tinkerspy/pinball/diptrace/png/controller02-pcb.png

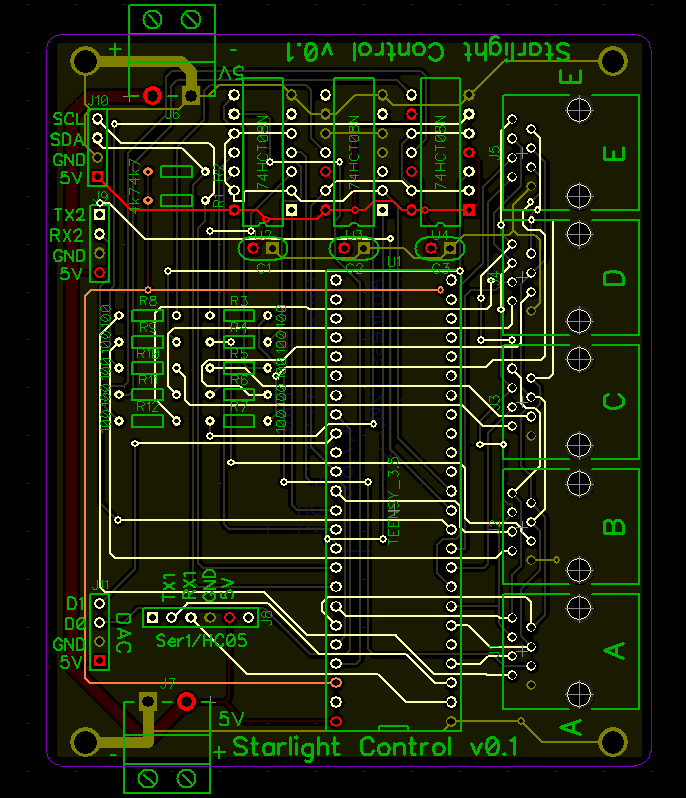
diptrace/png/controller02-pcb.png
