tinkerspy/pinball/diptrace/png/switchnodexl02-pcb.png

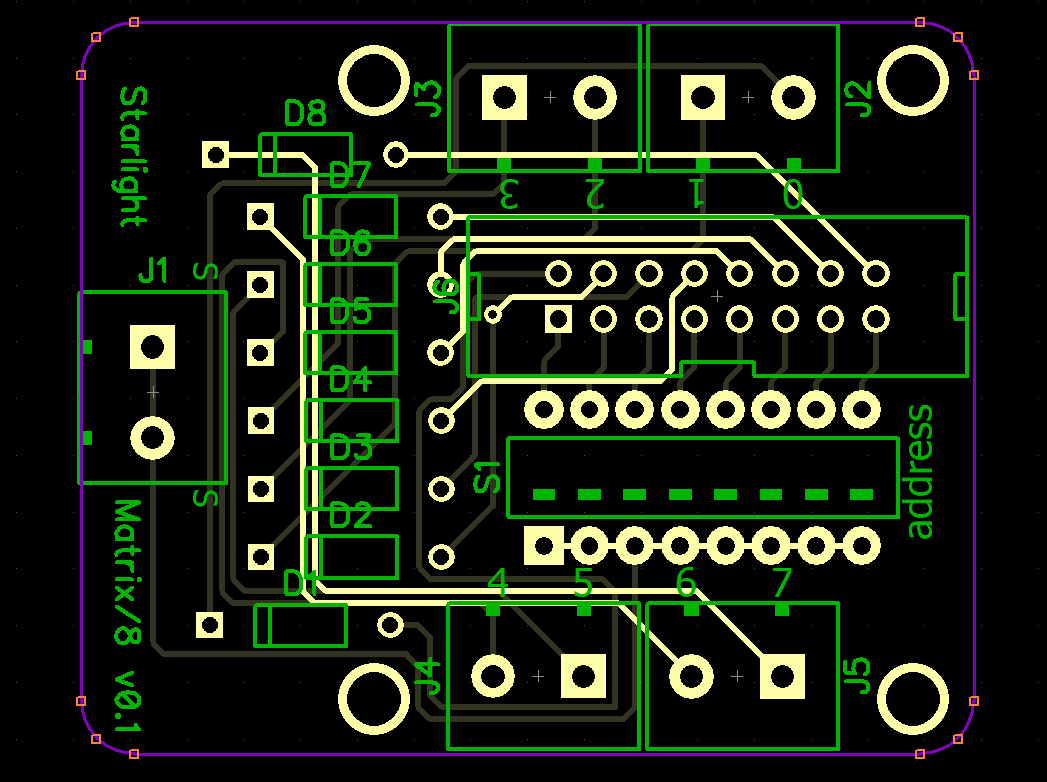
diptrace/png/switchnodexl02-pcb.png
