tinkerspy/pinball/firmware_custom.h

#pragma once

/* Custom firmware for the Atm_device programmable pinball device class
 *  
 *  tictactoe
 *  
 *  playfield.device( <switch-id> ); // Instantiates object
 *  playfield.device( <switch-id>, <led-id>, <firmware> ); // Initializes object
 *  
 */

namespace custom_firmware {

const char game_bytecode[] = R""""(
init, press_start, release_start, ball_exit, sub_wait_players, sub_wait_reset, sub_loop, \
sub_ball_loop, sub_player_loop, sub_core, sub_wait_playing, sub_wait_collecting, sub_press_start
out_init, out_enable, out_counter_reset, out_players_zero, out_ball_zero,\
out_player_zero, out_ball_adv, out_player_adv, out_3bonus, out_collect,\
out_kickoff, out_over, out_players_adv, out_disable, out_release
arg_collecting, arg_again, arg_counter0, arg_counter1,\
arg_counter2, arg_counter3, arg_counter4, arg_counter5
reg_state, reg_max_players, reg_no_of_players, reg_player, reg_no_of_balls,\
reg_ball, reg_ball_cntr
msg_init, msg_wait_start, msg_ball_loop, msg_player_loop, msg_counter_reset, msg_add_player


// TODO tilt!
sub_press_start
R, -1, -1, reg_ball_cntr       // Exit if we're already in play
>,  0, -1, 0
R, -1, -1, reg_no_of_players   // Exit 
=,  6,  0, 2
R, -1, -1, reg_max_players 
=,  6, -1, 0
R, -1, -1, reg_no_of_players
=,  5,  0, 2
R, -1, -1, reg_max_players
=,  5, -1, 0
R, -1, -1, reg_no_of_players
=,  4,  0, 2
R, -1, -1, reg_max_players
=,  4, -1, 0
R, -1, -1, reg_no_of_players
=,  3,  0, 2
R, -1, -1, reg_max_players
=,  3, -1, 0
R, -1, -1, reg_no_of_players
=,  2,  0, 2
R, -1, -1, reg_max_players
=,  2, -1, 0
R, -1, -1, reg_no_of_players
=,  1,  0, 2
R, -1, -1, reg_max_players
=,  1, -1, 0
R, -1, -1, reg_no_of_players
T, -1, -1, out_players_adv
I, -1, -1, 1
Q, reg_no_of_players, -1, msg_add_player;

init
T, -1, -1, out_init             
W, -1, -1, 100                
R, -1, -1, 0
D, -1, -1, reg_no_of_balls
R, -1, -1, 1
D, -1, -1, reg_max_players
R, -1, -1, 0
Z, -1, -1, 0
A, -1, -1, sub_loop;

sub_loop
T, -1, -1, out_over
R, -1, -1, reg_ball_cntr
Z, -1, -1, 0
R, -1, -1, reg_no_of_players
Z, -1, -1, 0
E, press_start, 0, 0            // Clear press event
Q, -1, -1, msg_wait_start
S, -1, -1, sub_wait_players     // Wait for a front button press to start game
W, -1, -1, 100
Q, -1, -1, msg_init
T, -1, -1, out_init
T, -1, -1, out_players_zero
T, -1, -1, out_ball_zero
T, -1, -1, out_counter_reset
S, -1, -1, sub_wait_reset
R, -1, -1, reg_no_of_balls
D, -1, -1, reg_ball
T, -1, -1, out_player_zero
S, -1, -1, sub_ball_loop
A, -1, -1, sub_loop;

sub_ball_loop
Q, reg_ball, -1, msg_ball_loop
R, -1, -1, reg_no_of_players
D, -1, -1, reg_player
T, -1, -1, out_player_zero
W, -1, -1, 11
S, -1, -1, sub_player_loop
W, -1, -1, 12
R, -1, -1, reg_ball
I, -1, -1, -1
=,  0, -1, 0
T, -1, -1, out_ball_adv
A, -1, -1, sub_ball_loop;

sub_player_loop
Q, reg_player, -1, msg_player_loop
S, -1, -1, sub_core
J, arg_again, -2, 0
R, -1, -1, reg_player
I, -1, -1, -1
=,  0, -1, 0
T, -1, -1, out_player_adv
A, -1, -1, sub_player_loop;

sub_core
W, -1, -1, 500
R, -1, -1, reg_ball
T,  1,  out_3bonus, -1
T, -1, -1, out_init
W, -1, -1, 100
T, -1, -1, out_kickoff
W, -1, -1, 1000
T, -1, -1, out_enable
W, -1, -1, 100
E, ball_exit, 0, 0                // Clear press_exit event
S, -1, -1, sub_wait_playing
T, -1, -1, out_disable
T, -1, -1, out_release
W, -1, -1, 100
T, -1, -1, out_collect
W, -1, -1, 100
S, -1, -1, sub_wait_collecting
W, -1, -1, 100
R, -1, -1, reg_ball_cntr
I, -1, -1, 1
=,  1,  0, -1
R, -1, -1, reg_no_of_players
D, -1, -1, reg_player;

sub_wait_players
R, -1, -1, reg_no_of_players
W, -1, -1, 0
E, press_start, 0, 2                // On event set no of players to 1
Z, -1, -1, 1
J, -1, -1, -1                       // and exit sub
A, -1, -1, sub_wait_players;        // else keep looping

sub_wait_reset                      // busy loop: waiting for counter reset to finish
Q, reg_max_players, -1, msg_counter_reset
W, -1, -1, 100
E, press_start, 0, 1                // On event increment no of players
S, -1, -1, sub_press_start
J, arg_counter0, -4, 0
J, arg_counter1, -5, 0
J, arg_counter2, -6, 0
J, arg_counter3, -7, 0
J, arg_counter4, -8, 0
J, arg_counter5, -9, 0;

sub_wait_playing                    // Central game loop: process ball_exit & frontbtn press
R, -1, -1, reg_no_of_players
W, -1, -1, 0
E, press_start, 0, 1                // On event set no of players to 1
S, -1, -1, sub_press_start
E, ball_exit, -1, -4;

sub_wait_collecting
W, -1, -1, 100
J, arg_collecting, -2, -1;
)"""";

const char std_game_symbin[] = {
  "\x78\x56\x34\x12\xb0\x00\x00\x00" "init\0press_start\0release_start\0ball_exit\0sub_wait_players\0sub_wait_reset\0sub_loop\0sub_ball_loop\0sub_player_loop\0sub_core\0sub_wait_playing\0sub_wait_collecting\0sub_press_start\0\0\0"
  "\x78\x56\x34\x12\xc8\x00\x00\x00" "out_init\0out_enable\0out_counter_reset\0out_players_zero\0out_ball_zero\0out_player_zero\0out_ball_adv\0out_player_adv\0out_3bonus\0out_collect\0out_kickoff\0out_over\0out_players_adv\0out_disable\0out_release\0\0\0\0"
  "\x78\x56\x34\x12\x68\x00\x00\x00" "arg_collecting\0arg_again\0arg_counter0\0arg_counter1\0arg_counter2\0arg_counter3\0arg_counter4\0arg_counter5\0\0"
  "\x78\x56\x34\x12\x60\x00\x00\x00" "reg_state\0reg_max_players\0reg_no_of_players\0reg_player\0reg_no_of_balls\0reg_ball\0reg_ball_cntr\0\0\0"
  "\x00\x00\x00\x00\x00\x00\x00\x00" "msg_init\0msg_wait_start\0msg_ball_loop\0msg_player_loop\0msg_counter_reset\0msg_add_player\0\0"
};

const uint16_t std_game_hexbin[] = {
  0x0089, 0x0000, 0x0000, 0x0000, 0x01B3, 0x01CD, 0x00AF, 0x0101, 0x0133, 0x0155, 0x01F7, 0x020D, 
  0x000F, 0xFFFF, 0x000C, 0x0052, 0xFFFF, 0xFFFF, 0x0006, 0x003E, 0x0000, 0xFFFF, 0x0000, 0x0052, 
  0xFFFF, 0xFFFF, 0x0002, 0x003D, 0x0006, 0x0000, 0x0002, 0x0052, 0xFFFF, 0xFFFF, 0x0001, 0x003D, 
  0x0006, 0xFFFF, 0x0000, 0x0052, 0xFFFF, 0xFFFF, 0x0002, 0x003D, 0x0005, 0x0000, 0x0002, 0x0052, 
  0xFFFF, 0xFFFF, 0x0001, 0x003D, 0x0005, 0xFFFF, 0x0000, 0x0052, 0xFFFF, 0xFFFF, 0x0002, 0x003D, 
  0x0004, 0x0000, 0x0002, 0x0052, 0xFFFF, 0xFFFF, 0x0001, 0x003D, 0x0004, 0xFFFF, 0x0000, 0x0052, 
  0xFFFF, 0xFFFF, 0x0002, 0x003D, 0x0003, 0x0000, 0x0002, 0x0052, 0xFFFF, 0xFFFF, 0x0001, 0x003D, 
  0x0003, 0xFFFF, 0x0000, 0x0052, 0xFFFF, 0xFFFF, 0x0002, 0x003D, 0x0002, 0x0000, 0x0002, 0x0052, 
  0xFFFF, 0xFFFF, 0x0001, 0x003D, 0x0002, 0xFFFF, 0x0000, 0x0052, 0xFFFF, 0xFFFF, 0x0002, 0x003D, 
  0x0001, 0x0000, 0x0002, 0x0052, 0xFFFF, 0xFFFF, 0x0001, 0x003D, 0x0001, 0xFFFF, 0x0000, 0x0052, 
  0xFFFF, 0xFFFF, 0x0002, 0x0054, 0xFFFF, 0xFFFF, 0x000C, 0x0049, 0xFFFF, 0xFFFF, 0x0001, 0x0051, 
  0x0002, 0xFFFF, 0x0005, 0xFFFF, 0x0000, 0x0054, 0xFFFF, 0xFFFF, 0x0000, 0x0057, 0xFFFF, 0xFFFF, 
  0x0064, 0x0052, 0xFFFF, 0xFFFF, 0x0000, 0x0044, 0xFFFF, 0xFFFF, 0x0004, 0x0052, 0xFFFF, 0xFFFF, 
  0x0001, 0x0044, 0xFFFF, 0xFFFF, 0x0001, 0x0052, 0xFFFF, 0xFFFF, 0x0000, 0x005A, 0xFFFF, 0xFFFF, 
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
  "\x78\x56\x34\x12\x28\x00\x00\x00" "init\0cycle\0sub_led0\0sub_led1\0sub_led2\0\0\0"
  "\x78\x56\x34\x12\x04\x00\x00\x00" "\0\0\0\0"
  "\x78\x56\x34\x12\x1c\x00\x00\x00" "arg_led0\0arg_led1\0arg_led2\0\0"
  "\x00\x00\x00\x00\x00\x00\x00\x00" "reg_t0\0reg_t1\0reg_t2\0\0"
};

const uint16_t std_animation_hexbin[] = {
  0x0007, 0x0019, 0x002F, 0x0051, 0x0073, 0xFFFF, 0x0000, 0x004C, 0xFFFF, 0xFFFF, 0x0000, 0x004C, 
  0xFFFF, 0xFFFF, 0x0001, 0x004C, 0xFFFF, 0xFFFF, 0x0002, 0x0041, 0xFFFF, 0xFFFF, 0x0001, 0xFFFF, 
  0x0001, 0x0057, 0xFFFF, 0xFFFF, 0x0064, 0x0053, 0xFFFF, 0xFFFF, 0x0002, 0x0053, 0xFFFF, 0xFFFF, 
  0x0003, 0x0053, 0xFFFF, 0xFFFF, 0x0004, 0x0041, 0xFFFF, 0xFFFF, 0x0001, 0xFFFF, 0x0002, 0x0052, 
  0xFFFF, 0xFFFF, 0x0000, 0x0049, 0xFFFF, 0xFFFF, 0xFFFF, 0x003C, 0x0001, 0x0000, 0xFFFF, 0x005A, 
  0xFFFF, 0xFFFF, 0x0008, 0x004A, 0x0000, 0x0000, 0x0002, 0x004C, 0xFFFF, 0xFFFF, 0x0000, 0x004A, 
  0xFFFF, 0xFFFF, 0xFFFF, 0x0048, 0xFFFF, 0xFFFF, 0x0000, 0xFFFF, 0x0003, 0x0052, 0xFFFF, 0xFFFF, 
  0x0001, 0x0049, 0xFFFF, 0xFFFF, 0xFFFF, 0x003C, 0x0001, 0x0000, 0xFFFF, 0x005A, 0xFFFF, 0xFFFF, 
  0x0005, 0x004A, 0x0001, 0x0000, 0x0002, 0x004C, 0xFFFF, 0xFFFF, 0x0001, 0x004A, 0xFFFF, 0xFFFF, 
  0xFFFF, 0x0048, 0xFFFF, 0xFFFF, 0x0001, 0xFFFF, 0x0004, 0x0052, 0xFFFF, 0xFFFF, 0x0002, 0x0049, 
  0xFFFF, 0xFFFF, 0xFFFF, 0x003C, 0x0001, 0x0000, 0xFFFF, 0x005A, 0xFFFF, 0xFFFF, 0x0007, 0x004A, 
  0x0002, 0x0000, 0x0002, 0x004C, 0xFFFF, 0xFFFF, 0x0002, 0x004A, 0xFFFF, 0xFFFF, 0xFFFF, 0x0048, 
  0xFFFF, 0xFFFF, 0x0002, 0xFFFF, 0xFFFF
};


// Williams OXO tic-tac-toe game

const char tictactoe_bytecode[] = R""""(
init, oxo_1o, oxo_1x, oxo_2o, oxo_2x, oxo_3o, oxo_3x, oxo_4, oxo_5, oxo_6, oxo_7, oxo_8, oxo_9,\
toggle, collect, single, triple sub_collect, sub_match_123, sub_match_456, sub_match_789,\
sub_match_147, sub_match_258, sub_match_369, sub_match_159, sub_match_357, sub_match_all, sub_clear
out_score, out_win_row, out_win_all, out_collect
arg_1a, arg_1b, arg_1c, arg_2a, arg_2b, arg_2c, arg_3a, arg_3b, arg_3c, arg_4a, arg_4b, arg_4c,\
arg_5a, arg_5b, arg_5c, arg_6a, arg_6b, arg_6c, arg_7a, arg_7b, arg_7c, arg_8a, arg_8b, arg_8c,\
arg_9a, arg_9b, arg_9c, arg_x, arg_o, arg_triple, arg_collect


init
L, -1, -1, arg_collect
S, -1, -1, sub_clear;

oxo_1o
J, arg_1a, -1, 0
J, arg_1b, -1, 0
H, -1, -1, arg_1a
H, -1, -1, arg_1c
S, -1, -1, sub_match_123
S, -1, -1, sub_match_147
S, -1, -1, sub_match_159
S, -1, -1, sub_match_all;

oxo_1x
J, arg_1a, -1, 0
J, arg_1b, -1, 0
H, -1, -1, arg_1b
S, -1, -1, sub_match_123
S, -1, -1, sub_match_147
S, -1, -1, sub_match_159
S, -1, -1, sub_match_all;

oxo_2o
J, arg_2a, -1, 0
J, arg_2b, -1, 0
H, -1, -1, arg_2a
H, -1, -1, arg_2c
S, -1, -1, sub_match_123
S, -1, -1, sub_match_258
S, -1, -1, sub_match_all;

oxo_2x
J, arg_2a, -1, 0
J, arg_2b, -1, 0
H, -1, -1, arg_2b
S, -1, -1, sub_match_123
S, -1, -1, sub_match_258
S, -1, -1, sub_match_all;

oxo_3o
J, arg_3a, -1, 0
J, arg_3b, -1, 0
H, -1, -1, arg_3a
H, -1, -1, arg_3c
S, -1, -1, sub_match_123
S, -1, -1, sub_match_369
S, -1, -1, sub_match_357
S, -1, -1, sub_match_all;

oxo_3x
J, arg_3a, -1, 0
J, arg_3b, -1, 0
H, -1, -1, arg_3b
S, -1, -1, sub_match_123
S, -1, -1, sub_match_369
S, -1, -1, sub_match_357
S, -1, -1, sub_match_all;

oxo_4
J, arg_4a, -1, 0
J, arg_4b, -1, 0
H, arg_x, arg_4b, arg_4a
H, arg_x, arg_4b, arg_4c
S, -1, -1, sub_match_147
S, -1, -1, sub_match_456
S, -1, -1, sub_match_all;

oxo_5
J, arg_5a, -1, 0
J, arg_5b, -1, 0
H, arg_x, arg_5b, arg_5a
H, arg_x, arg_5b, arg_5c
S, -1, -1, sub_match_159
S, -1, -1, sub_match_258
S, -1, -1, sub_match_357
S, -1, -1, sub_match_456
S, -1, -1, sub_match_all;

oxo_6
J, arg_6a, -1, 0
J, arg_6b, -1, 0
H, arg_x, arg_6b, arg_6a
H, arg_x, arg_6b, arg_6c
S, -1, -1, sub_match_369
S, -1, -1, sub_match_456
S, -1, -1, sub_match_all;

oxo_7
J, arg_7a, -1, 0
J, arg_7b, -1, 0
H, arg_x, arg_7b, arg_7a
H, arg_x, arg_7b, arg_7c
S, -1, -1, sub_match_789
S, -1, -1, sub_match_147
S, -1, -1, sub_match_357
S, -1, -1, sub_match_all;

oxo_8
J, arg_8a, -1, 0
J, arg_8b, -1, 0
H, arg_x, arg_8b, arg_8a
H, arg_x, arg_8b, arg_8c
S, -1, -1, sub_match_258
S, -1, -1, sub_match_789
S, -1, -1, sub_match_all;

oxo_9
J, arg_9a, -1, 0
J, arg_9b, -1, 0
H, arg_x, arg_9b, arg_9a
H, arg_x, arg_9b, arg_9c
S, -1, -1, sub_match_159
S, -1, -1, sub_match_369
S, -1, -1, sub_match_789
S, -1, -1, sub_match_all;

toggle
J, arg_x, 0, 3
L, -1, -1, arg_x
H, -1, -1, arg_o
J, -1, -1, -1
L, -1, -1, arg_o
H, -1, -1, arg_x;

single
L, -1, -1, arg_triple;

triple
H, -1, -1, arg_triple;

collect
H, -1, -1, arg_collect
S, -1, -1, sub_collect
J, arg_triple, 0, 4
W, -1, -1, 500
S, -1, -1, sub_collect
W, -1, -1, 500
S, -1, -1, sub_collect
Z, -1, -1, 0
L, -1, -1, arg_collect;

sub_match_123
J, arg_1a, 0,  2
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
  0xFFFF, 0x000E, 0x0048, 0xFFFF, 0xFFFF, 0x001E, 0x0053, 0xFFFF, 0xFFFF, 0x0011, 0x004A, 0x001D, 
  0x0000, 0x0004, 0x0057, 0xFFFF, 0xFFFF, 0x01F4, 0x0053, 0xFFFF, 0xFFFF, 0x0011, 0x0057, 0xFFFF, 
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
};

};
