tinkerspy/pinball/Singularity.h

#pragma once

#include <Automaton.h>
#include "IO.hpp"
#include "Atm_switch_matrix.hpp"
#include "Atm_my_command.hpp"
#include "Atm_led_matrix.hpp"
#include "IO_Adafruit_NeoPixel.hpp"
#include "Atm_device.hpp"
#include "firmware_standard.hpp"
#include "Symbolic_Machine.hpp"
#include "Library.hpp"
